pkropf/exuro/pycon 2011/poster session.graffle/image6.jpg

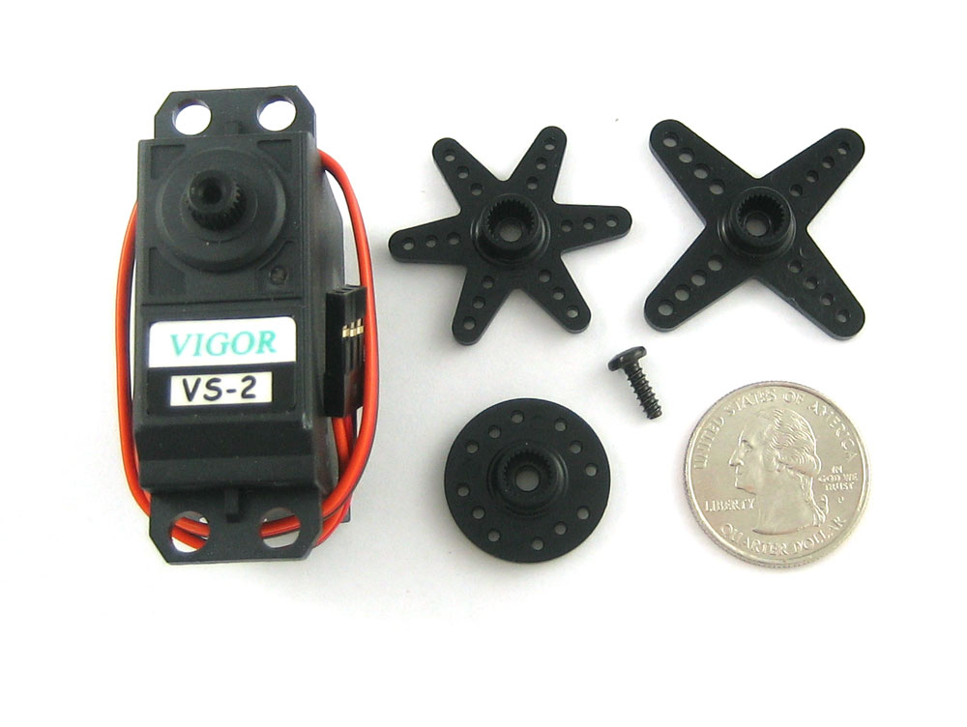
pycon 2011/poster session.graffle/image6.jpg
