pkropf/exuro/kinect/depth.jpg

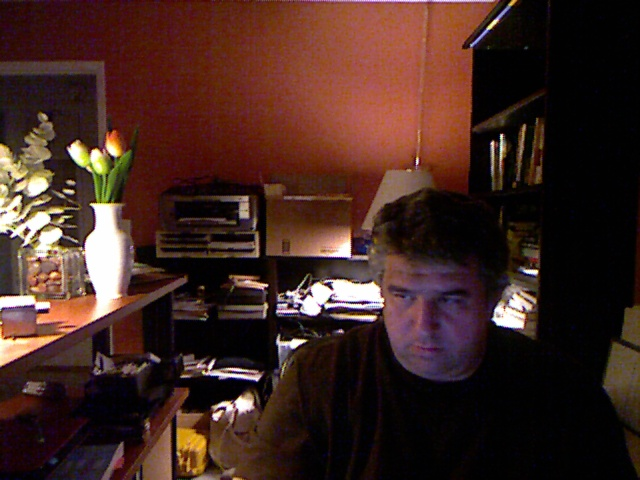
kinect/depth.jpg
