pkropf/exuro/pycon 2011/poster session.graffle/image2.jpg

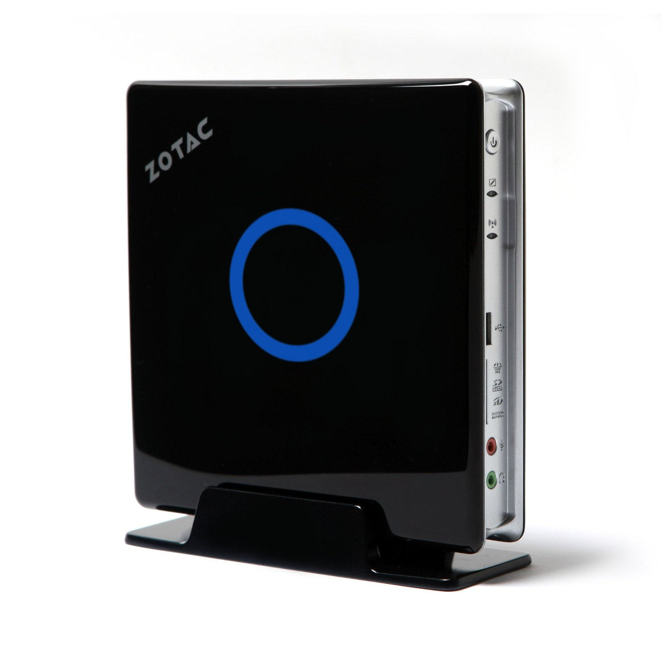
pycon 2011/poster session.graffle/image2.jpg
