pkropf/exuro/pycon 2011/poster session.graffle/image5.jpg

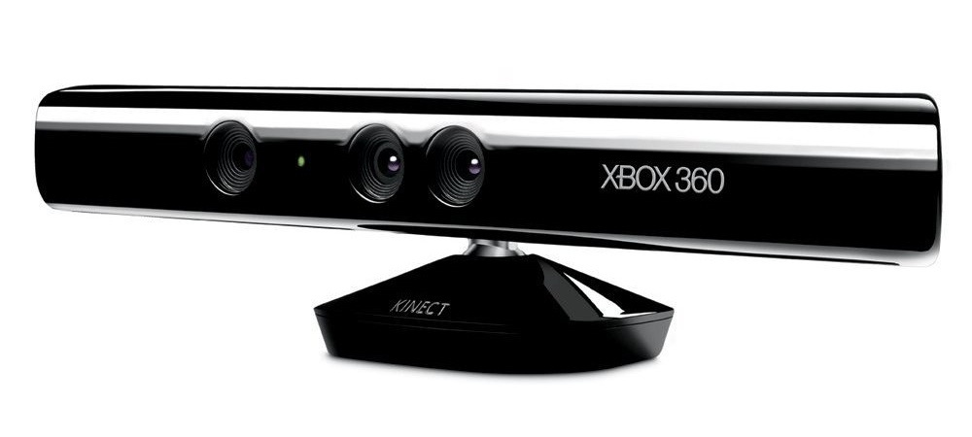
pycon 2011/poster session.graffle/image5.jpg
