pkropf/exuro/pycon 2011/poster session.graffle/image7.jpg

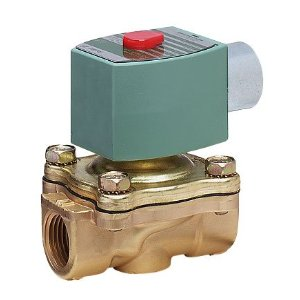
pycon 2011/poster session.graffle/image7.jpg
