pkropf/exuro/pycon 2011/poster session.graffle/image9.jpg

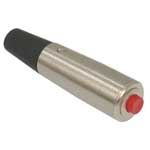
pycon 2011/poster session.graffle/image9.jpg
