pkropf/exuro/pycon 2011/poster session.graffle/image10.jpeg

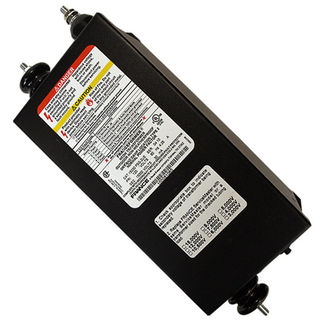
pycon 2011/poster session.graffle/image10.jpeg
