pkropf/exuro/pycon 2011/poster session.graffle/image11.jpg

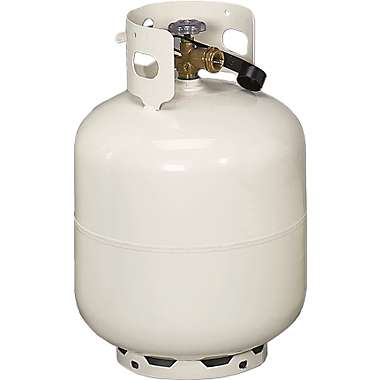
pycon 2011/poster session.graffle/image11.jpg
