pkropf/exuro/pycon 2011/poster session.graffle/image21.png

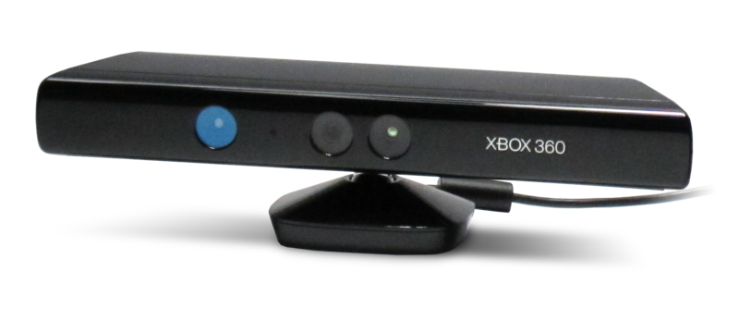
pycon 2011/poster session.graffle/image21.png
