pkropf/exuro/pycon 2011/poster session.graffle/image22.JPG

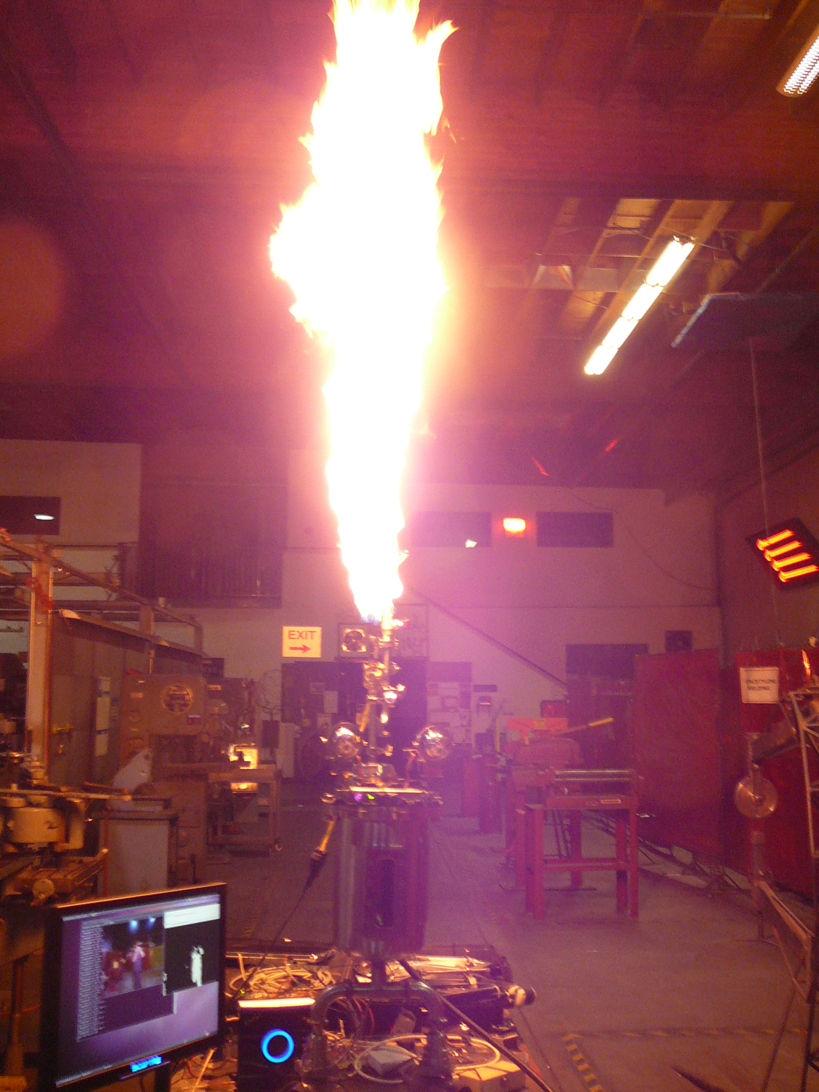
pycon 2011/poster session.graffle/image22.JPG
