pkropf/exuro/pycon 2011/poster session.graffle/image23.jpg

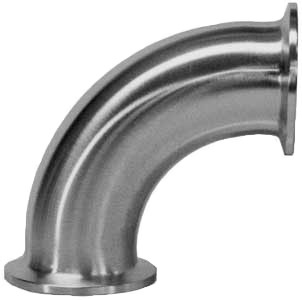
pycon 2011/poster session.graffle/image23.jpg
