pkropf/exuro/threshold1.screenflow/thumbnail.jpg

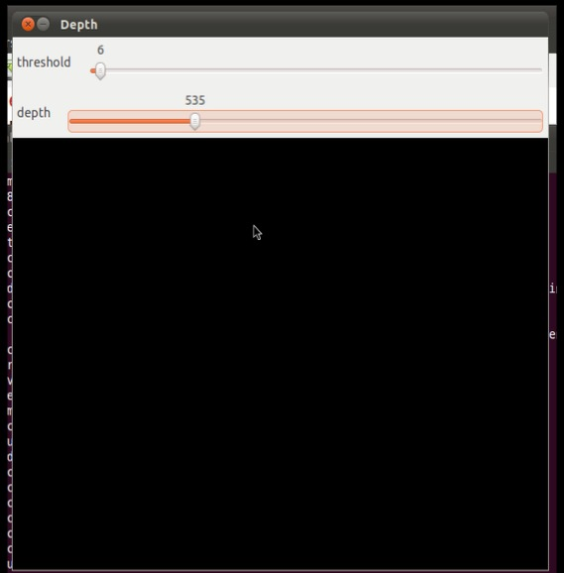
threshold1.screenflow/thumbnail.jpg
