pkropf/exuro/get_twitter_access_keys.py

#!/usr/bin/env python

import tweepy

CONSUMER_KEY = 'tilHukjV3YlPfgnvmsDQ'
CONSUMER_SECRET = 'l6bfewmxPHG3fpPl4NoDWBCcMJ233RqvNGVSmyKfU'

auth = tweepy.OAuthHandler(CONSUMER_KEY, CONSUMER_SECRET)
auth_url = auth.get_authorization_url()
print 'Please authorize: ' + auth_url
verifier = raw_input('PIN: ').strip()
auth.get_access_token(verifier)
print "ACCESS_KEY = '%s'" % auth.access_token.key
print "ACCESS_SECRET = '%s'" % auth.access_token.secret
